dl2fw/LDMOSPA/images/20240617_192155.jpg

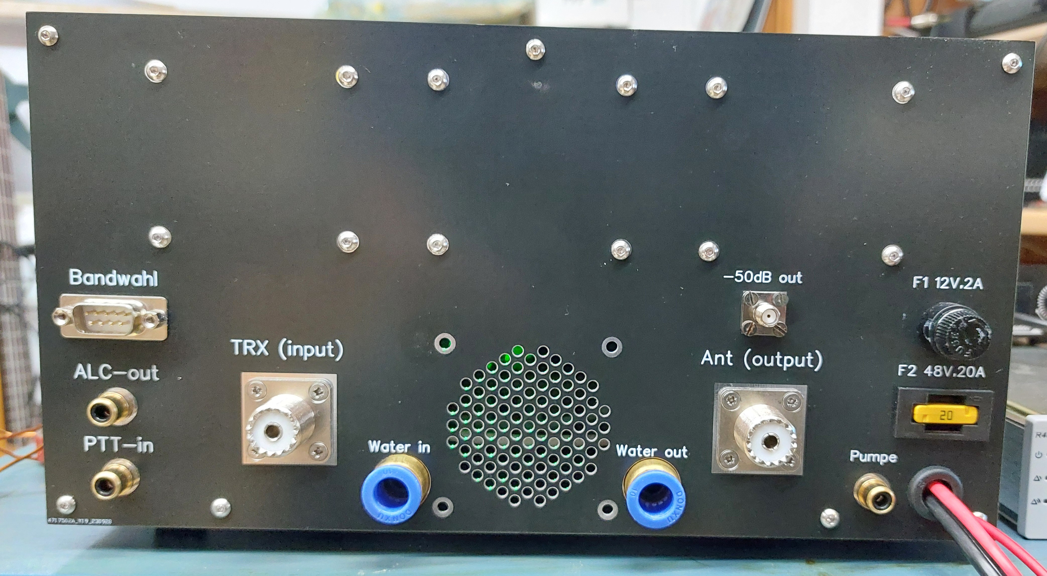
images/20240617_192155.jpg
